sekigon-gonnoc/Kugel-doc/img/kugel_1.JPG

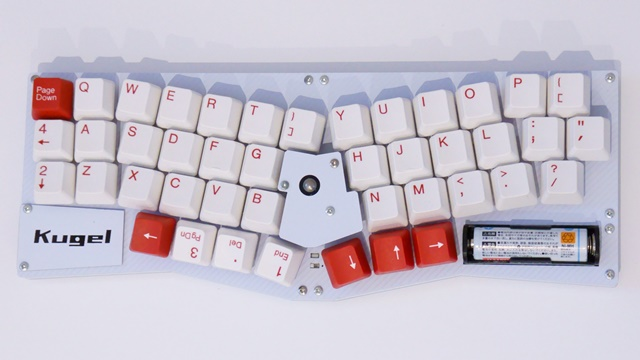
img/kugel_1.JPG
