sekigon-gonnoc/Kugel-doc/img/kugel_2.jpg

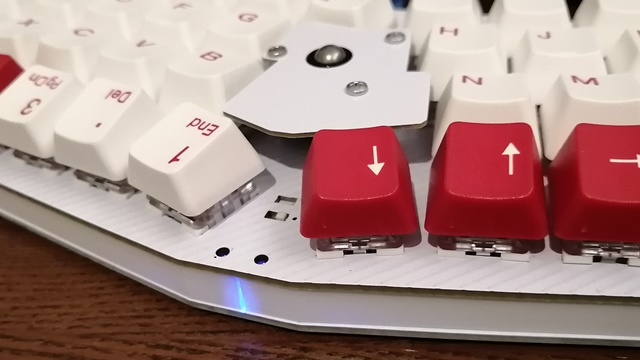
img/kugel_2.jpg
