sekigon-gonnoc/Kugel-doc/img/part008.jpg

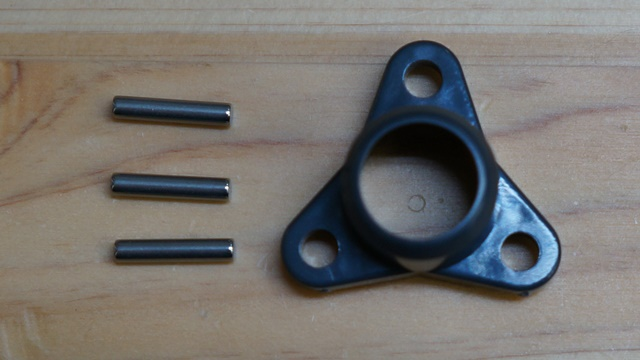
img/part008.jpg
