sekigon-gonnoc/Kugel-doc/img/part013.jpg

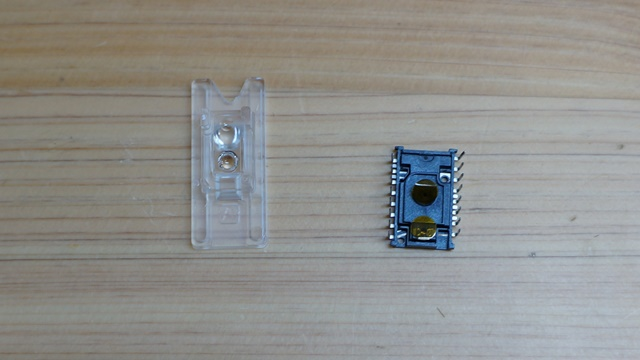
img/part013.jpg
