sekigon-gonnoc/Kugel-doc/img/part015.jpg

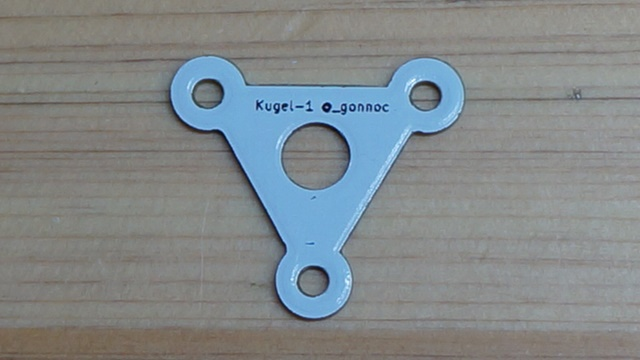
img/part015.jpg
