sekigon-gonnoc/Kugel-doc/img/part017.jpg

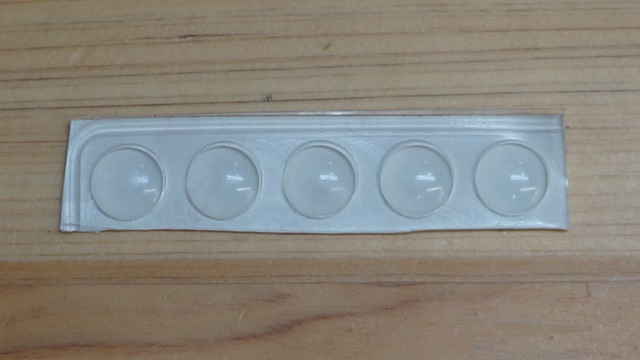
img/part017.jpg
