sekigon-gonnoc/Kugel-doc/img/part018.jpg

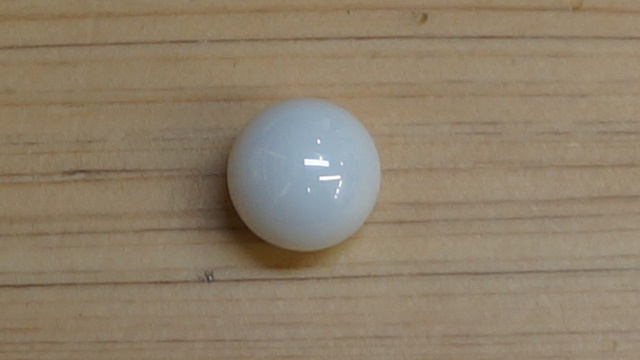
img/part018.jpg
