sekigon-gonnoc/Kugel-doc/img/build001.jpg

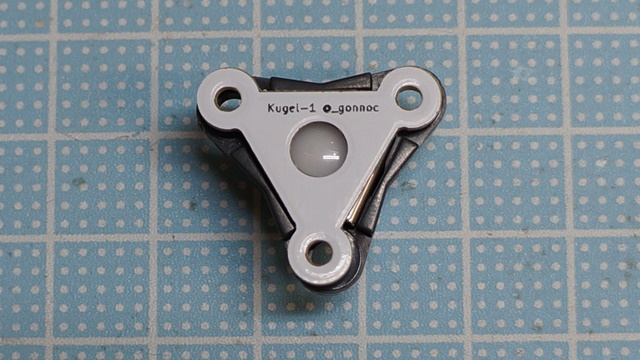
img/build001.jpg
