sekigon-gonnoc/Kugel-doc/img/build002.jpg

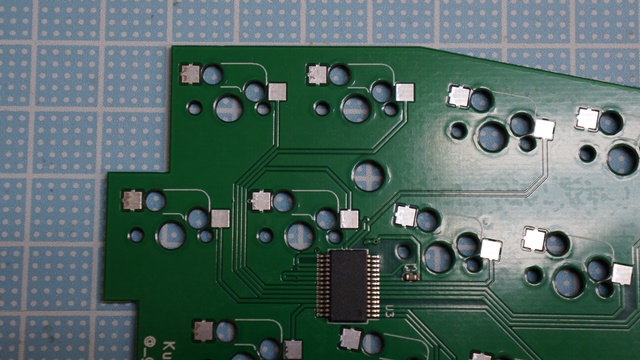
img/build002.jpg
