sekigon-gonnoc/Kugel-doc/img/build005.jpg

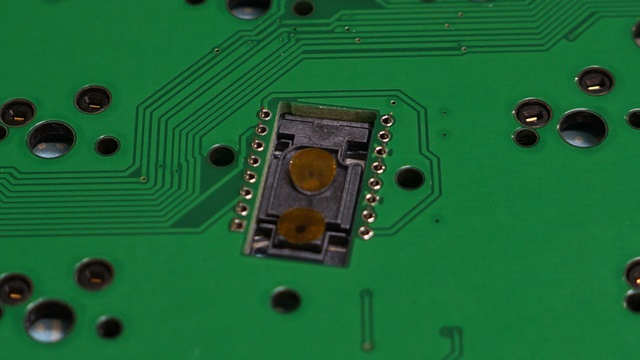
img/build005.jpg
