sekigon-gonnoc/Kugel-doc/img/build006.jpg

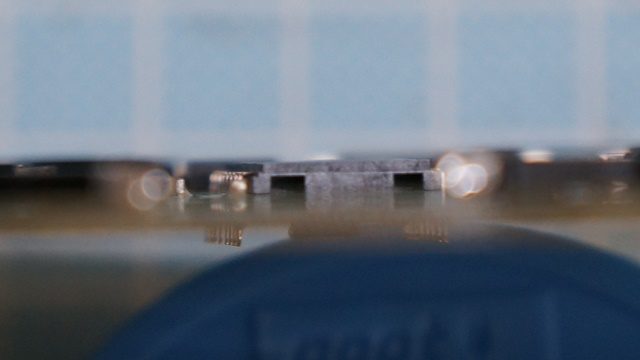
img/build006.jpg
