sekigon-gonnoc/Kugel-doc/img/build007.jpg

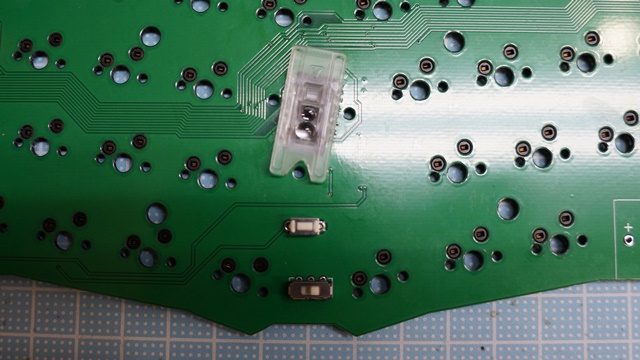
img/build007.jpg
