sekigon-gonnoc/Kugel-doc/img/build010.jpg

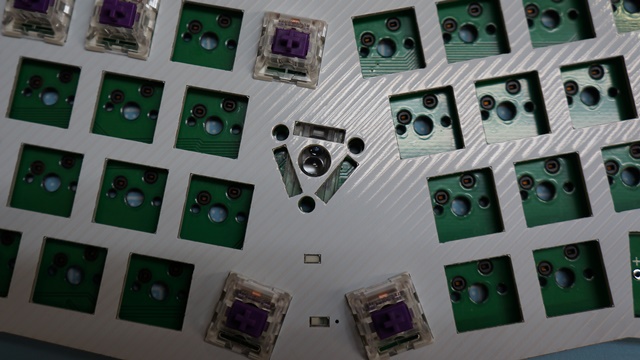
img/build010.jpg
