sekigon-gonnoc/Kugel-doc/img/build011.jpg

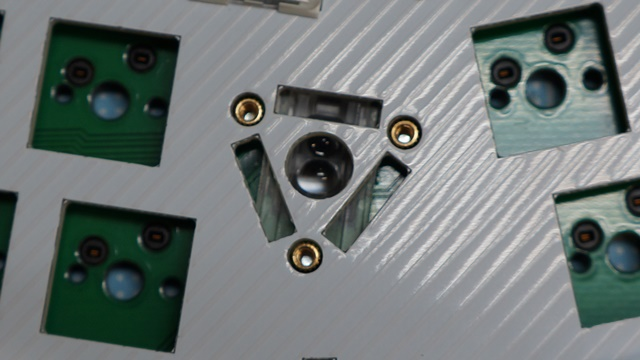
img/build011.jpg
