sekigon-gonnoc/Kugel-doc/img/build017.jpg

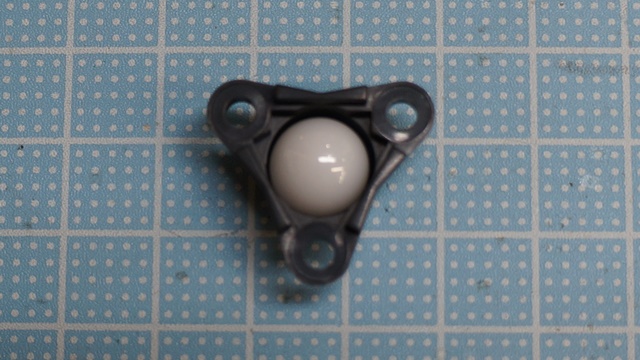
img/build017.jpg
