sekigon-gonnoc/Kugel-doc/img/build018.jpg

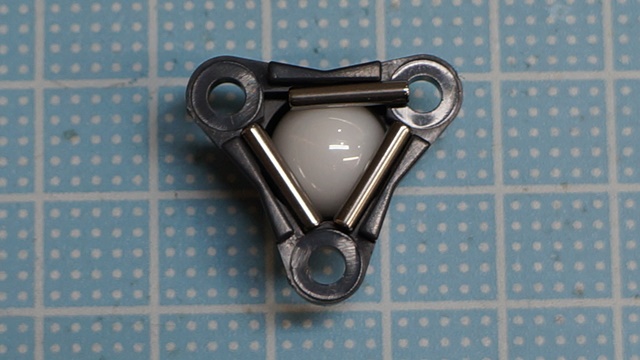
img/build018.jpg
