sekigon-gonnoc/Kugel-doc/img/build020.jpg

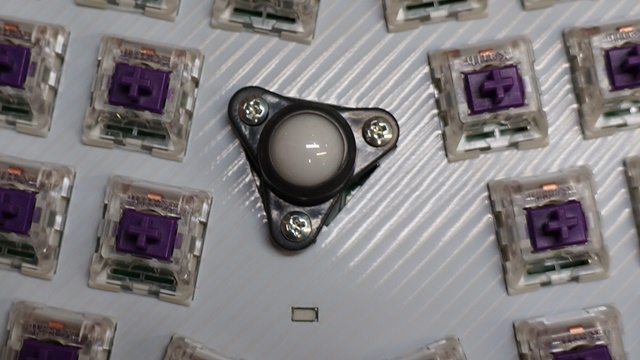
img/build020.jpg
