sekigon-gonnoc/Kugel-doc/img/build030.jpg

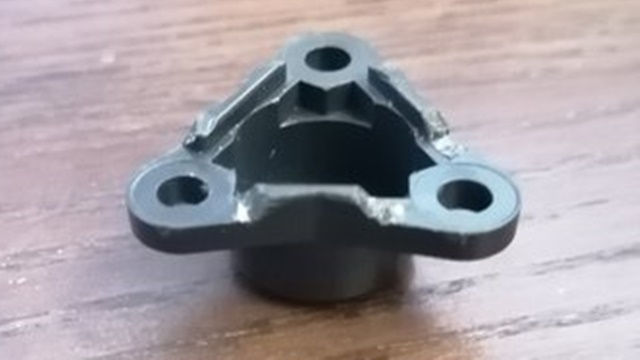
img/build030.jpg
